Michelingumman/Battery-Managment-System-for-Leakage-Current/volvo-schematic.asc

R1: res; 100
R2: res; 93.3
R3: res; 330
R4: res; 1.2k
R5: res; 330
R6: res; 4.7k
R7: res; 220
U1: lm358
U2: lm358
V1: voltage; 5
V2: voltage; 1
Named nets: 0, 5V
.dc V2 -75m 75m 0.001
