Michelingumman/Battery-Managment-System-for-Leakage-Current/rapport/schematic/schematic.kicad_pcb

## KiCad design schematics/ESPtemp.kicad_sch

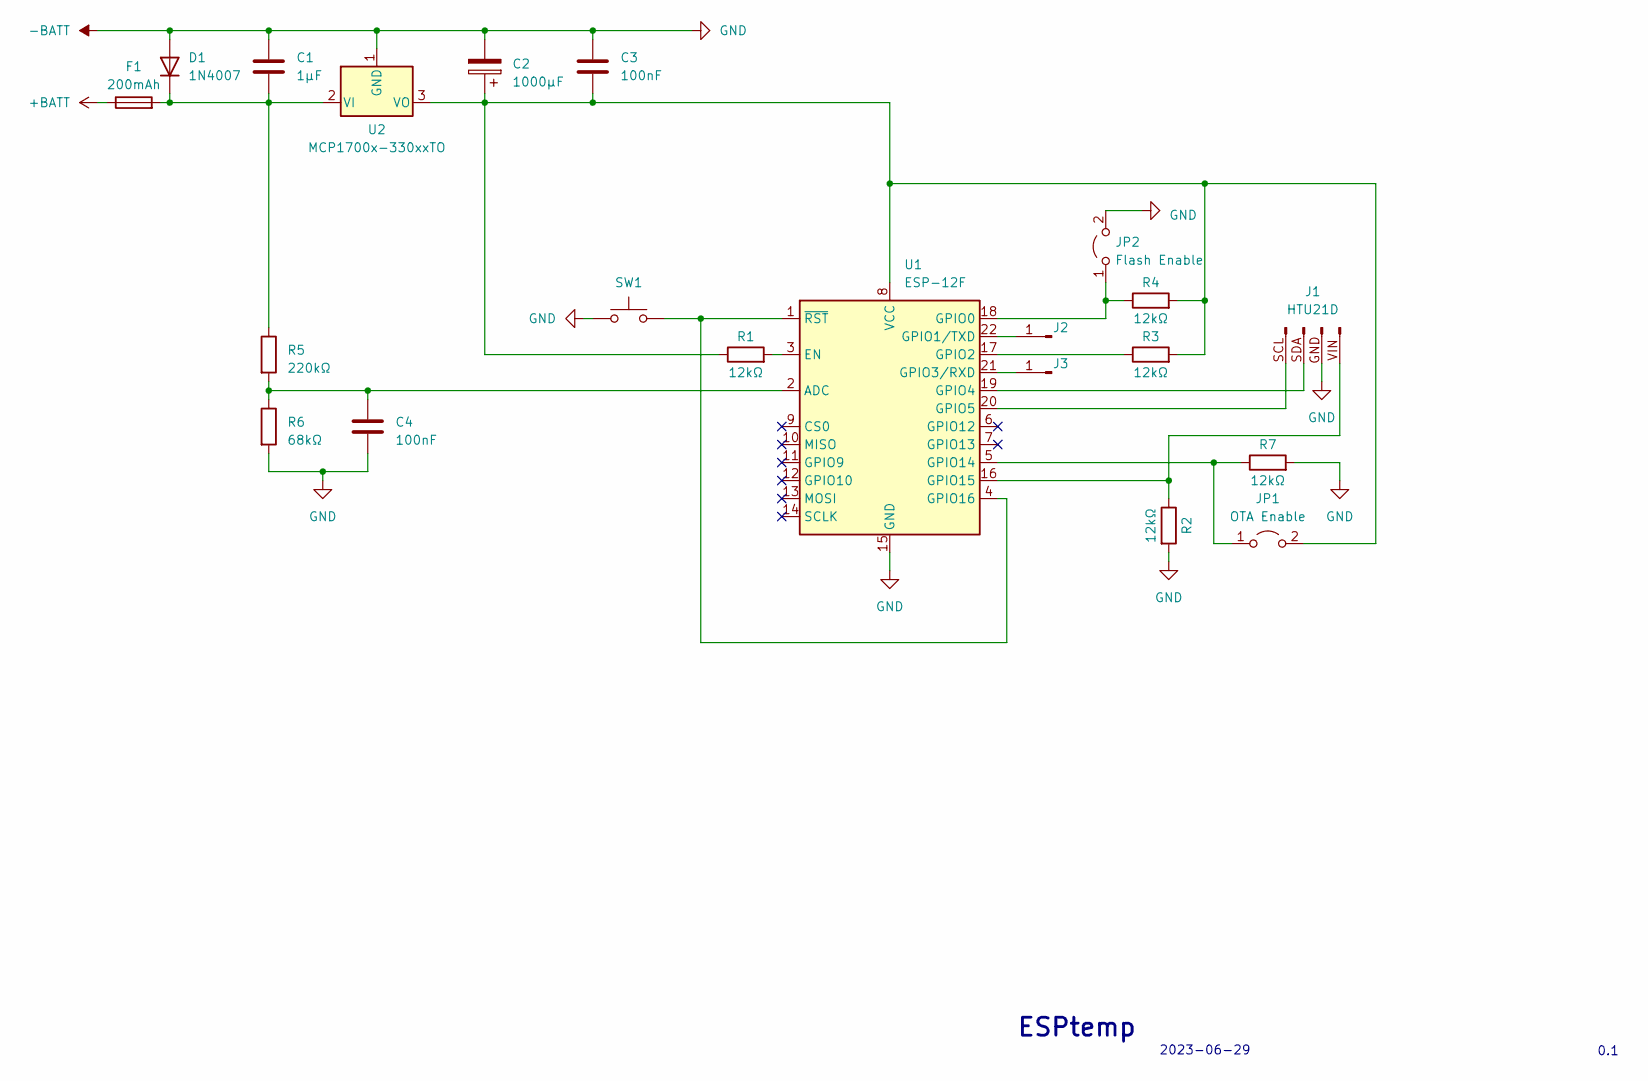
[picture p11: schematic ESPtemp.kicad_sch]

Parts:
C1: 1μF
C2: 1000μF
C3, C4: 100nF
D1: 1N4007; D_DO-41_SOD81_P10.16mm_Horizontal
F1: 200mAh
J1: HTU21D
J2, J3: (no value)
JP1: OTA Enable
JP2: Flash Enable
R1, R2, R3, R4, R7: 12kΩ
R5: 220kΩ
R6: 68kΩ
SW1: SW_Push
U1: ESP-12F; ESP-12E
U2: MCP1700x-330xxTO; TO-92_Inline

Connections:
+BATT: F1.1
-BATT: C1.1, C2.2, C3.1, C4.2, D1.2 (A), J1.GND (Pin_2), JP2.2 (B), R2.2, R6.2, R7.2, SW1.1, U1.15 (GND), U2.1 (GND)
unnamed: C1.2, D1.1 (K), F1.2, R5.1, U2.2 (VI)
unnamed: C2.1, C3.2, JP1.2 (B), R1.1, R3.2, R4.2, U1.8 (VCC), U2.3 (VO)
unnamed: C4.1, R5.2, R6.1, U1.2 (ADC)
unnamed: J1.SCL (Pin_4), U1.20 (GPIO5)
unnamed: J1.SDA (Pin_3), U1.19 (GPIO4)
unnamed: J1.VIN (Pin_1), R2.1, U1.16 (GPIO15)
unnamed: J2.1, U1.22 (GPIO1/TXD)
unnamed: J3.1, U1.21 (GPIO3/RXD)
unnamed: JP1.1 (A), R7.1, U1.5 (GPIO14)
unnamed: JP2.1 (A), R4.1, U1.18 (GPIO0)
unnamed: R1.2, U1.3 (EN)
unnamed: R3.1, U1.17 (GPIO2)
unnamed: SW1.2, U1.1 (~RST), U1.4 (GPIO16)

Notes on the sheet:
ESPtemp
0.1
2023-06-29
