Michelingumman/Battery-Managment-System-for-Leakage-Current/src/image_data.h

// image_data.h
#ifndef IMAGE_DATA_H
#define IMAGE_DATA_H

static const unsigned char PROGMEM image_Release_arrow_18x15_bits[] = {0x00,0x60,0x00,0x00,0x50,0x00,0x00,0x48,0x00,0x00,0x44,0x00,0x7f,0xd2,0x00,0x80,0x19,0x00,0xbf,0xfc,0x80,0xbf,0xfe,0x40,0xbf,0xfc,0x80,0x80,0x19,0x00,0x7f,0xd2,0x00,0x00,0x44,0x00,0x00,0x48,0x00,0x00,0x50,0x00,0x00,0x60,0x00};

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


// om vscode tycker denna blir ett "PROBLEM" så skit i det.. bara en varning! ;)
#endif
